ComNets-Bremen/WUSN/PCB-Enclosures/MoleNet_v6/Mounting_Plate/readme.txt

only Simple_Molenet_V6_Mount_Single_Screw_Pillars.stl tested. 
printed with 15% infill no support needed.
