ComNets-Bremen/WUSN/src/ATMEGA-based/MoleNet_2.0/decagon_5tm/README.md

# Decagon 5TM sensor Libarary

The library for temperature and volumetric content of water sensor, Decagon 5TM

### Version
1.0.0
