ComNets-Bremen/WUSN/src/ATMEGA-based/MoleNet_2.0/external_eeprom/README.md

# MoleNet Sensor Node EEPROM Libarary

The library external EEPROM (25LC1024) operations related to MoleNet Sensor Node.

### Version
1.0.0
