ComNets-Bremen/WUSN/src/ATMEGA-based/MoleNet_2.0/molenet_sensor_node/README.md

# Main MoleNet Sensor Node Libarary

The main library for MolneNet Sensor Node. It conatins all the functionalities 
of Multihop routing.

### Version
1.0.0
