ComNets-Bremen/WUSN/PCB-Layouts/MoleNet_v6.1/Readme.md

This folder contain Kicad files of Molenet V6.1 Board.
