ComNets-Bremen/WUSN/src/ATMEGA-based/MoleNet_2.0/serial_print/README.md

# Optimized Serial Print

A RAM optimized Serial print for Arduino. `Serial.print()` function in arduino consume
RAM to print the strings. These files provides method to print strings by storing 
then in program memory. More details can found in this like.

    http://www.utopiamechanicus.com/article/low-memory-serial-print/

### Version
1.0.0
