ComNets-Bremen/WUSN/experiments/LoRa_Gateway_for_WUSN/Modified Libraries/README.md

# Modified Libraries

This folder contains the RFM69 library modified, to work on a LoPy4.
Find the original library here: https://github.com/LowPowerLab/RFM69
