ComNets-Bremen/WUSN/experiments/LoRa_Gateway_for_WUSN/Field_Experiment/Field_experiment_2020_06_12.ods

jsonData.app_id | jsonData.dev_id | jsonData.hardware_serial | jsonData.port | jsonData.counter | jsonData.payload_raw | jsonData.payload_decoded | jsonData.metadata.time | jsonData.metadata.frequency | jsonData.metadata.modulation | jsonData.metadata.data_rate | jsonData.metadata.coding_rate | jsonData.metadata.downlink_url | gateway.gtw_id | gateway.timestamp | gateway.channel | gateway.rssi | gateway.snr | gateway.latitude | gateway.longitude | gateway.altitude | gateway.gtw_id | gateway.timestamp | gateway.channel | gateway.rssi | gateway.snr | gateway.latitude | gateway.longitude | gateway.altitude | gateway.gtw_id | gateway.timestamp | gateway.channel | gateway.rssi | gateway.snr | gateway.latitude | gateway.longitude | gateway.altitude
test_04_02_19 | pycomarduino | 0058924AB98D5AD4 | 1 | 0 | TW9pbgAAAAAAAAAAAAAAAAAAAAAAAAAAAAAAAAAAAAAAAAAAAAAAAA== | Moin | 2020-06-12T15:04:56.676741706Z | 867,3 | LORA | SF7BW125 | 4/5 | undefined | eui-fcc23dfffe0b696a | 2011301563 | 4 | -117 | -6,2 | undefined | undefined | undefined | eui-b827ebfffef74e1a | 1101593699 | 4 | -81 | 9,8 | undefined | undefined | undefined
test_04_02_19 | pycomarduino | 0058924AB98D5AD4 | 1 | 1 | WzJdIEQyMC8wNS8xOCB0MTI6MDAgVzAwMDAgVDAwMDAgPyAxICAgAA== | [2] D20/05/18 t12:00 W0000 T0000 ? 1 | 2020-06-12T15:05:29.272881041Z | 868,1 | LORA | SF7BW125 | 4/5 | undefined | eui-fcc23dfffe0b696a | 2043860939 | 0 | -117 | -4 | undefined | undefined | undefined | eui-b827ebfffef74e1a | 1134153083 | 0 | -82 | 9,2 | undefined | undefined | undefined
test_04_02_19 | pycomarduino | 0058924AB98D5AD4 | 1 | 2 | WzNdIEQyMC8wNS8xOCB0MTI6MDAgVzAwMDAgVDAwMDAgPyAxICAgAA== | [3] D20/05/18 t12:00 W0000 T0000 ? 1 | 2020-06-12T15:06:55.994188636Z | 868,3 | LORA | SF7BW125 | 4/5 | undefined | eui-b827ebfffef74e1a | 1220915163 | 1 | -84 | 9 | undefined | undefined | undefined
test_04_02_19 | pycomarduino | 0058924AB98D5AD4 | 1 | 3 | WzRdIEQyMC8wNS8xOCB0MTI6MDAgVzAwMDAgVDAwMDAgPyAxICAgAA== | [4] D20/05/18 t12:00 W0000 T0000 ? 1 | 2020-06-12T15:08:07.594137698Z | 867,5 | LORA | SF7BW125 | 4/5 | undefined | eui-fcc23dfffe0b696a | 2202222652 | 5 | -116 | -4 | undefined | undefined | undefined | eui-b827ebfffef74e1a | 1292514876 | 5 | -81 | 7 | undefined | undefined | undefined
test_04_02_19 | pycomarduino | 0058924AB98D5AD4 | 1 | 4 | WzVdIEQyMC8wNS8xOCB0MTI6MDAgVzAwMDAgVDAwMDAgPyAxICAgAA== | [5] D20/05/18 t12:00 W0000 T0000 ? 1 | 2020-06-12T15:09:34.050602207Z | 868,5 | LORA | SF7BW125 | 4/5 | undefined | eui-fcc23dfffe0b696a | 2288667515 | 2 | -112 | -2 | undefined | undefined | undefined | eui-b827ebfffef74e1a | 1378959771 | 2 | -83 | 7,8 | undefined | undefined | undefined
test_04_02_19 | pycomarduino | 0058924AB98D5AD4 | 1 | 5 | WzJdIEQyMC8wNS8xOCB0MTI6MDAgVzAwMDAgVDAwMDAgPyAxICAgAA== | [2] D20/05/18 t12:00 W0000 T0000 ? 1 | 2020-06-12T16:05:29.255052341Z | 868,1 | LORA | SF7BW125 | 4/5 | undefined | eui-b827ebfffef74e1a | 439193619 | 0 | -85 | 10 | undefined | undefined | undefined
test_04_02_19 | pycomarduino | 0058924AB98D5AD4 | 1 | 6 | WzNdIEQyMC8wNS8xOCB0MTI6MDAgVzAwMDAgVDAwMDAgPyAxICAgAA== | [3] D20/05/18 t12:00 W0000 T0000 ? 1 | 2020-06-12T16:06:55.988793539Z | 867,7 | LORA | SF7BW125 | 4/5 | undefined | eui-fcc23dfffe0b696a | 1435643132 | 6 | -113 | -4 | undefined | undefined | undefined | eui-b827ebfffef74e1a | 525936972 | 6 | -83 | 9,2 | undefined | undefined | undefined
test_04_02_19 | pycomarduino | 0058924AB98D5AD4 | 1 | 7 | WzRdIEQyMC8wNS8xOCB0MTI6MDAgVzAwMDAgVDAwMDAgPyAxICAgAA== | [4] D20/05/18 t12:00 W0000 T0000 ? 1 | 2020-06-12T16:08:07.601479262Z | 868,3 | LORA | SF7BW125 | 4/5 | undefined | eui-b827ebfffef74e1a | 597545867 | 1 | -83 | 9,2 | undefined | undefined | undefined
test_04_02_19 | pycomarduino | 0058924AB98D5AD4 | 1 | 8 | WzVdIEQyMC8wNS8xOCB0MTI6MDAgVzAwMDAgVDAwMDAgPyAxICAgAA== | [5] D20/05/18 t12:00 W0000 T0000 ? 1 | 2020-06-12T16:09:34.045542755Z | 868,5 | LORA | SF7BW125 | 4/5 | undefined | eui-fcc23dfffe0b696a | 1593703123 | 2 | -112 | -0,2 | undefined | undefined | undefined | eui-b827ebfffef74e1a | 683997035 | 2 | -81 | 7,8 | undefined | undefined | undefined
test_04_02_19 | pycomarduino | 0058924AB98D5AD4 | 1 | 9 | WzVdIEQyMC8wNS8xOCB0MTI6MDAgVzAwMDAgVDAwMDAgPyAxICAgAA== | [5] D20/05/18 t12:00 W0000 T0000 ? 1 | 2020-06-12T17:21:05.049491599Z | 867,9 | LORA | SF7BW125 | 4/5 | undefined | eui-fcc23dfffe0a9698 | 1591886324 | 7 | -116 | -5,5 | undefined | undefined | undefined | eui-b827ebfffef74e1a | 680034476 | 7 | -85 | 10,2 | undefined | undefined | undefined
test_04_02_19 | pycomarduino | 0058924AB98D5AD4 | 1 | 10 | WzVdIEQyMC8wNS8xOCB0MTI6MDAgVzAwMDAgVDAwMDAgPyAxICAgAA== | [5] D20/05/18 t12:00 W0000 T0000 ? 1 | 2020-06-12T18:32:39.87590631Z | 868,1 | LORA | SF7BW125 | 4/5 | undefined | eui-fcc23dfffe0b696a | 1589587211 | 0 | -117 | -1,8 | undefined | undefined | undefined | eui-b827ebfffef74e1a | 679885035 | 0 | -84 | 9,5 | undefined | undefined | undefined
test_04_02_19 | pycomarduino | 0058924AB98D5AD4 | 1 | 11 | WzJdIEQyMC8wNS8xOCB0MTI6MDAgVzAwMDAgVDAwMDAgPyAxICAgAA== | [2] D20/05/18 t12:00 W0000 T0000 ? 1 | 2020-06-12T19:05:29.263679511Z | 868,3 | LORA | SF7BW125 | 4/5 | undefined | eui-b827ebfffef74e1a | 2649283859 | 1 | -81 | 9,8 | undefined | undefined | undefined
test_04_02_19 | pycomarduino | 0058924AB98D5AD4 | 1 | 12 | WzNdIEQyMC8wNS8xOCB0MTI6MDAgVzAwMDAgVDAwMDAgPyAxICAgAA== | [3] D20/05/18 t12:00 W0000 T0000 ? 1 | 2020-06-12T19:06:55.94949052Z | 867,1 | LORA | SF7BW125 | 4/5 | undefined | eui-fcc23dfffe0a9698 | 3647817851 | 3 | -117 | -5 | undefined | undefined | undefined | eui-fcc23dfffe0b696a | 3645671747 | 3 | -117 | -0,5 | undefined | undefined | undefined | eui-b827ebfffef74e1a | 2735970507 | 3 | -89 | 11 | undefined | undefined | undefined
test_04_02_19 | pycomarduino | 0058924AB98D5AD4 | 1 | 13 | WzRdIEQyMC8wNS8xOCB0MTI6MDAgVzAwMDAgVDAwMDAgPyAxICAgAA== | [4] D20/05/18 t12:00 W0000 T0000 ? 1 | 2020-06-12T19:08:07.598150806Z | 868,5 | LORA | SF7BW125 | 4/5 | undefined | eui-b827ebfffef74e1a | 2807605883 | 2 | -80 | 7,2 | undefined | undefined | undefined
test_04_02_19 | pycomarduino | 0058924AB98D5AD4 | 1 | 14 | WzVdIEQyMC8wNS8xOCB0MTI6MDAgVzAwMDAgVDAwMDAgPyAxICAgAA== | [5] D20/05/18 t12:00 W0000 T0000 ? 1 | 2020-06-12T19:09:34.056058936Z | 868,1 | LORA | SF7BW125 | 4/5 | undefined | eui-b827ebfffef74e1a | 2894068995 | 0 | -84 | 9,8 | undefined | undefined | undefined
test_04_02_19 | pycomarduino | 0058924AB98D5AD4 | 1 | 15 | WzVdIEQyMC8wNS8xOCB0MTI6MDAgVzAwMDAgVDAwMDAgPyAxICAgAA== | [5] D20/05/18 t12:00 W0000 T0000 ? 1 | 2020-06-12T20:21:01.304674464Z | 867,3 | LORA | SF7BW125 | 4/5 | undefined | eui-fcc23dfffe0a9698 | 3798202899 | 4 | -116 | -7,8 | undefined | undefined | undefined | eui-fcc23dfffe0b696a | 3796057891 | 4 | -113 | -0,2 | undefined | undefined | undefined | eui-b827ebfffef74e1a | 2886358707 | 4 | -84 | 10 | undefined | undefined | undefined
test_04_02_19 | pycomarduino | 0058924AB98D5AD4 | 1 | 16 | WzVdIEQyMC8wNS8xOCB0MTI6MDAgVzAwMDAgVDAwMDAgPyAxICAgAA== | [5] D20/05/18 t12:00 W0000 T0000 ? 1 | 2020-06-12T21:32:32.91198065Z | 868,3 | LORA | SF7BW125 | 4/5 | undefined | eui-fcc23dfffe0b696a | 3792697227 | 1 | -113 | -3,8 | undefined | undefined | undefined | eui-b827ebfffef74e1a | 2882999995 | 1 | -83 | 10,2 | undefined | undefined | undefined
test_04_02_19 | pycomarduino | 0058924AB98D5AD4 | 1 | 17 | WzJdIEQyMC8wNS8xOCB0MTI6MDAgVzAwMDAgVDAwMDAgPyAxICAgAA== | [2] D20/05/18 t12:00 W0000 T0000 ? 1 | 2020-06-12T22:05:29.287404391Z | 868,5 | LORA | SF7BW125 | 4/5 | undefined | eui-fcc23dfffe0b696a | 1474103859 | 2 | -111 | 2 | undefined | undefined | undefined | eui-b827ebfffef74e1a | 564407523 | 2 | -81 | 7,8 | undefined | undefined | undefined
test_04_02_19 | pycomarduino | 0058924AB98D5AD4 | 1 | 18 | WzNdIEQyMC8wNS8xOCB0MTI6MDAgVzAwMDAgVDAwMDAgPyAxICAgAA== | [3] D20/05/18 t12:00 W0000 T0000 ? 1 | 2020-06-12T22:06:55.918812572Z | 867,5 | LORA | SF7BW125 | 4/5 | undefined | eui-fcc23dfffe0b696a | 1560732596 | 5 | -112 | -1,2 | undefined | undefined | undefined | eui-b827ebfffef74e1a | 651036300 | 5 | -83 | 8,2 | undefined | undefined | undefined
test_04_02_19 | pycomarduino | 0058924AB98D5AD4 | 1 | 19 | WzRdIEQyMC8wNS8xOCB0MTI6MDAgVzAwMDAgVDAwMDAgPyAxICAgAA== | [4] D20/05/18 t12:00 W0000 T0000 ? 1 | 2020-06-12T22:08:07.582433212Z | 868,1 | LORA | SF7BW125 | 4/5 | undefined | eui-fcc23dfffe0b696a | 1632394187 | 0 | -115 | -2,8 | undefined | undefined | undefined | eui-b827ebfffef74e1a | 722697915 | 0 | -84 | 10,8 | undefined | undefined | undefined
test_04_02_19 | pycomarduino | 0058924AB98D5AD4 | 1 | 20 | WzVdIEQyMC8wNS8xOCB0MTI6MDAgVzAwMDAgVDAwMDAgPyAxICAgAA== | [5] D20/05/18 t12:00 W0000 T0000 ? 1 | 2020-06-12T22:09:34.052301362Z | 868,3 | LORA | SF7BW125 | 4/5 | undefined | eui-fcc23dfffe0b696a | 1718869131 | 1 | -105 | 1,5 | undefined | undefined | undefined | eui-b827ebfffef74e1a | 809172899 | 1 | -81 | 9,8 | undefined | undefined | undefined
test_04_02_19 | pycomarduino | 0058924AB98D5AD4 | 1 | 21 | WzVdIEQyMC8wNS8xOCB0MTI6MDAgVzAwMDAgVDAwMDAgPyAxICAgAA== | [5] D20/05/18 t12:00 W0000 T0000 ? 1 | 2020-06-12T23:21:00.383448831Z | 867,7 | LORA | SF7BW125 | 4/5 | undefined | eui-b827ebfffef74e1a | 800529868 | 6 | -82 | 8,2 | undefined | undefined | undefined
test_04_02_19 | pycomarduino | 0058924AB98D5AD4 | 1 | 22 | WzVdIEQyMC8wNS8xOCB0MTI6MDAgVzAwMDAgVDAwMDAgPyAxICAgAA== | [5] D20/05/18 t12:00 W0000 T0000 ? 1 | 2020-06-13T00:32:30.636119936Z | 868,5 | LORA | SF7BW125 | 4/5 | undefined | eui-fcc23dfffe0b696a | 1705506987 | 2 | -112 | -2 | undefined | undefined | undefined | eui-b827ebfffef74e1a | 795814563 | 2 | -82 | 8,2 | undefined | undefined | undefined
test_04_02_19 | pycomarduino | 0058924AB98D5AD4 | 1 | 23 | WzJdIEQyMC8wNS8xOCB0MTI6MDAgVzAwMDAgVDAwMDAgPyAxICAgAA== | [2] D20/05/18 t12:00 W0000 T0000 ? 1 | 2020-06-13T01:05:29.312525431Z | 868,1 | LORA | SF7BW125 | 4/5 | undefined | eui-b827ebfffef74e1a | 2774495755 | 0 | -84 | 9,2 | undefined | undefined | undefined
test_04_02_19 | pycomarduino | 0058924AB98D5AD4 | 1 | 24 | WzNdIEQyMC8wNS8xOCB0MTI6MDAgVzAwMDAgVDAwMDAgPyAxICAgAA== | [3] D20/05/18 t12:00 W0000 T0000 ? 1 | 2020-06-13T01:06:55.893936757Z | 867,9 | LORA | SF7BW125 | 4/5 | undefined | eui-fcc23dfffe0b696a | 3770757604 | 7 | -116 | -3,8 | undefined | undefined | undefined | eui-b827ebfffef74e1a | 2861066076 | 7 | -87 | 9,5 | undefined | undefined | undefined
test_04_02_19 | pycomarduino | 0058924AB98D5AD4 | 1 | 25 | WzRdIEQyMC8wNS8xOCB0MTI6MDAgVzAwMDAgVDAwMDAgPyAxICAgAA== | [4] D20/05/18 t12:00 W0000 T0000 ? 1 | 2020-06-13T01:08:07.566586655Z | 868,3 | LORA | SF7BW125 | 4/5 | undefined | eui-b827ebfffef74e1a | 2932753875 | 1 | -83 | 10 | undefined | undefined | undefined
test_04_02_19 | pycomarduino | 0058924AB98D5AD4 | 1 | 26 | WzVdIEQyMC8wNS8xOCB0MTI6MDAgVzAwMDAgVDAwMDAgPyAxICAgAA== | [5] D20/05/18 t12:00 W0000 T0000 ? 1 | 2020-06-13T01:09:34.06488205Z | 868,5 | LORA | SF7BW125 | 4/5 | undefined | eui-b827ebfffef74e1a | 3019240427 | 2 | -83 | 7,8 | undefined | undefined | undefined
test_04_02_19 | pycomarduino | 0058924AB98D5AD4 | 1 | 27 | WzVdIEQyMC8wNS8xOCB0MTI6MDAgVzAwMDAgVDAwMDAgPyAxICAgAA== | [5] D20/05/18 t12:00 W0000 T0000 ? 1 | 2020-06-13T02:20:56.05140405Z | 867,1 | LORA | SF7BW125 | 4/5 | undefined | eui-fcc23dfffe0a9698 | 3918102363 | 3 | -116 | -6,5 | undefined | undefined | undefined | eui-fcc23dfffe0b696a | 3915962563 | 3 | -116 | -1,2 | undefined | undefined | undefined | eui-b827ebfffef74e1a | 3006272939 | 3 | -85 | 9,5 | undefined | undefined | undefined
test_04_02_19 | pycomarduino | 0058924AB98D5AD4 | 1 | 28 | WzVdIEQyMC8wNS8xOCB0MTI6MDAgVzAwMDAgVDAwMDAgPyAxICAgAA== | [5] D20/05/18 t12:00 W0000 T0000 ? 1 | 2020-06-13T03:32:24.678205638Z | 868,1 | LORA | SF7BW125 | 4/5 | undefined | eui-b827ebfffef74e1a | 2999922915 | 0 | -82 | 9 | undefined | undefined | undefined
test_04_02_19 | pycomarduino | 0058924AB98D5AD4 | 1 | 29 | WzJdIEQyMC8wNS8xOCB0MTI6MDAgVzAwMDAgVDAwMDAgPyAxICAgAA== | [2] D20/05/18 t12:00 W0000 T0000 ? 1 | 2020-06-13T04:05:29.332817207Z | 868,3 | LORA | SF7BW125 | 4/5 | undefined | eui-b827ebfffef74e1a | 689618019 | 1 | -83 | 9,2 | undefined | undefined | undefined
test_04_02_19 | pycomarduino | 0058924AB98D5AD4 | 1 | 30 | WzNdIEQyMC8wNS8xOCB0MTI6MDAgVzAwMDAgVDAwMDAgPyAxICAgAA== | [3] D20/05/18 t12:00 W0000 T0000 ? 1 | 2020-06-13T04:06:55.84183936Z | 867,3 | LORA | SF7BW125 | 4/5 | undefined | eui-fcc23dfffe0b696a | 1685816123 | 4 | -112 | 0 | undefined | undefined | undefined | eui-b827ebfffef74e1a | 776129171 | 4 | -85 | 9,8 | undefined | undefined | undefined
test_04_02_19 | pycomarduino | 0058924AB98D5AD4 | 1 | 31 | WzRdIEQyMC8wNS8xOCB0MTI6MDAgVzAwMDAgVDAwMDAgPyAxICAgAA== | [4] D20/05/18 t12:00 W0000 T0000 ? 1 | 2020-06-13T04:08:07.556456043Z | 868,5 | LORA | SF7BW125 | 4/5 | undefined | eui-fcc23dfffe0a9698 | 1759668403 | 2 | -113 | -8,2 | undefined | undefined | undefined | eui-fcc23dfffe0b696a | 1757530195 | 2 | -112 | -1 | undefined | undefined | undefined | eui-b827ebfffef74e1a | 847843267 | 2 | -80 | 7 | undefined | undefined | undefined
test_04_02_19 | pycomarduino | 0058924AB98D5AD4 | 1 | 32 | WzVdIEQyMC8wNS8xOCB0MTI6MDAgVzAwMDAgVDAwMDAgPyAxICAgAA== | [5] D20/05/18 t12:00 W0000 T0000 ? 1 | 2020-06-13T04:09:34.060531823Z | 868,1 | LORA | SF7BW125 | 4/5 | undefined | eui-fcc23dfffe0b696a | 1844028411 | 0 | -115 | -4,8 | undefined | undefined | undefined | eui-b827ebfffef74e1a | 934341515 | 0 | -83 | 9,8 | undefined | undefined | undefined
test_04_02_19 | pycomarduino | 0058924AB98D5AD4 | 1 | 33 | WzVdIEQyMC8wNS8xOCB0MTI6MDAgVzAwMDAgVDAwMDAgPyAxICAgAA== | [5] D20/05/18 t12:00 W0000 T0000 ? 1 | 2020-06-13T05:20:56.244774296Z | 867,5 | LORA | SF7BW125 | 4/5 | undefined | eui-fcc23dfffe0b696a | 1831248988 | 5 | -112 | -3,2 | undefined | undefined | undefined | eui-b827ebfffef74e1a | 921563900 | 5 | -85 | 7,2 | undefined | undefined | undefined
test_04_02_19 | pycomarduino | 0058924AB98D5AD4 | 1 | 34 | WzVdIEQyMC8wNS8xOCB0MTI6MDAgVzAwMDAgVDAwMDAgPyAxICAgAA== | [5] D20/05/18 t12:00 W0000 T0000 ? 1 | 2020-06-13T06:32:24.231663194Z | 868,3 | LORA | SF7BW125 | 4/5 | undefined | eui-fcc23dfffe0b696a | 1824268339 | 1 | -112 | -1,5 | undefined | undefined | undefined | eui-b827ebfffef74e1a | 914585115 | 1 | -80 | 9,5 | undefined | undefined | undefined
test_04_02_19 | pycomarduino | 0058924AB98D5AD4 | 1 | 35 | WzJdIEQyMC8wNS8xOCB0MTI6MDAgVzAwMDAgVDAwMDAgPyAxICAgAA== | [2] D20/05/18 t12:00 W0000 T0000 ? 1 | 2020-06-13T07:05:29.3548985Z | 868,5 | LORA | SF7BW125 | 4/5 | undefined | eui-fcc23dfffe0b696a | 3809387403 | 2 | -111 | 0,8 | undefined | undefined | undefined | eui-b827ebfffef74e1a | 2899705067 | 2 | -80 | 7,8 | undefined | undefined | undefined
test_04_02_19 | pycomarduino | 0058924AB98D5AD4 | 1 | 36 | WzNdIEQyMC8wNS8xOCB0MTI6MDAgVzAwMDAgVDAwMDAgPyAxICAgAA== | [3] D20/05/18 t12:00 W0000 T0000 ? 1 | 2020-06-13T07:06:55.860422855Z | 867,7 | LORA | SF7BW125 | 4/5 | undefined | eui-b827ebfffef74e1a | 2986157332 | 6 | -83 | 9,8 | undefined | undefined | undefined
test_04_02_19 | pycomarduino | 0058924AB98D5AD4 | 1 | 37 | WzRdIEQyMC8wNS8xOCB0MTI6MDAgVzAwMDAgVDAwMDAgPyAxICAgAA== | [4] D20/05/18 t12:00 W0000 T0000 ? 1 | 2020-06-13T07:08:07.554054722Z | 868,1 | LORA | SF7BW125 | 4/5 | undefined | eui-fcc23dfffe0b696a | 3967580563 | 0 | -117 | -4,8 | undefined | undefined | undefined | eui-b827ebfffef74e1a | 3057898307 | 0 | -85 | 9,8 | undefined | undefined | undefined
test_04_02_19 | pycomarduino | 0058924AB98D5AD4 | 1 | 38 | WzVdIEQyMC8wNS8xOCB0MTI6MDAgVzAwMDAgVDAwMDAgPyAxICAgAA== | [5] D20/05/18 t12:00 W0000 T0000 ? 1 | 2020-06-13T07:09:34.063335579Z | 868,3 | LORA | SF7BW125 | 4/5 | undefined | eui-fcc23dfffe0b696a | 4054090227 | 1 | -113 | -2,5 | undefined | undefined | undefined | eui-b827ebfffef74e1a | 3144408011 | 1 | -84 | 9,5 | undefined | undefined | undefined
test_04_02_19 | pycomarduino | 0058924AB98D5AD4 | 1 | 39 | WzJdIEQyMC8wNS8xOCB0MTI6MDAgVzAwMDAgVDAwMDAgPyAxICAgAA== | [2] D20/05/18 t12:00 W0000 T0000 ? 1 | 2020-06-13T08:05:29.362372982Z | 867,9 | LORA | SF7BW125 | 4/5 | undefined | eui-fcc23dfffe0b696a | 3114427308 | 7 | -117 | -3 | undefined | undefined | undefined | eui-b827ebfffef74e1a | 2204746620 | 7 | -85 | 10,5 | undefined | undefined | undefined
test_04_02_19 | pycomarduino | 0058924AB98D5AD4 | 1 | 40 | WzNdIEQyMC8wNS8xOCB0MTI6MDAgVzAwMDAgVDAwMDAgPyAxICAgAA== | [3] D20/05/18 t12:00 W0000 T0000 ? 1 | 2020-06-13T08:06:55.796875119Z | 868,5 | LORA | SF7BW125 | 4/5 | undefined | eui-fcc23dfffe0b696a | 3200860539 | 2 | -112 | 1,2 | undefined | undefined | undefined | eui-b827ebfffef74e1a | 2291179891 | 2 | -83 | 8,2 | undefined | undefined | undefined
test_04_02_19 | pycomarduino | 0058924AB98D5AD4 | 1 | 41 | WzRdIEQyMC8wNS8xOCB0MTI6MDAgVzAwMDAgVDAwMDAgPyAxICAgAA== | [4] D20/05/18 t12:00 W0000 T0000 ? 1 | 2020-06-13T08:08:07.544424964Z | 868,1 | LORA | SF7BW125 | 4/5 | undefined | eui-fcc23dfffe0b696a | 3272610443 | 0 | -116 | -2,8 | undefined | undefined | undefined | eui-b827ebfffef74e1a | 2362929827 | 0 | -85 | 9,5 | undefined | undefined | undefined
test_04_02_19 | pycomarduino | 0058924AB98D5AD4 | 1 | 42 | WzVdIEQyMC8wNS8xOCB0MTI6MDAgVzAwMDAgVDAwMDAgPyAxICAgAA== | [5] D20/05/18 t12:00 W0000 T0000 ? 1 | 2020-06-13T08:09:34.058278605Z | 867,1 | LORA | SF7BW125 | 4/5 | undefined | eui-fcc23dfffe0a9698 | 3361258531 | 3 | -117 | -7 | undefined | undefined | undefined | eui-fcc23dfffe0b696a | 3359123771 | 3 | -114 | -1,2 | undefined | undefined | undefined | eui-b827ebfffef74e1a | 2449443203 | 3 | -87 | 9,2 | undefined | undefined | undefined
test_04_02_19 | pycomarduino | 0058924AB98D5AD4 | 1 | 43 | WzVdIEQyMC8wNS8xOCB0MTI6MDAgVzAwMDAgVDAwMDAgPyAxICAgAA== | [5] D20/05/18 t12:00 W0000 T0000 ? 1 | 2020-06-13T09:20:59.247299721Z | 868,3 | LORA | SF7BW125 | 4/5 | undefined | eui-b827ebfffef74e1a | 2439661731 | 1 | -81 | 9 | undefined | undefined | undefined
test_04_02_19 | pycomarduino | 0058924AB98D5AD4 | 1 | 44 | WzJdIEQyMC8wNS8xOCB0MTI6MDAgVzAwMDAgVDAwMDAgPyAxICAgAA== | [2] D20/05/18 t12:00 W0000 T0000 ? 1 | 2020-06-13T10:05:29.377044179Z | 868,5 | LORA | SF7BW125 | 4/5 | undefined | eui-fcc23dfffe0b696a | 1724505787 | 2 | -112 | -0,2 | undefined | undefined | undefined | eui-b827ebfffef74e1a | 814828315 | 2 | -81 | 6,8 | undefined | undefined | undefined
test_04_02_19 | pycomarduino | 0058924AB98D5AD4 | 1 | 45 | WzNdIEQyMC8wNS8xOCB0MTI6MDAgVzAwMDAgVDAwMDAgPyAxICAgAA== | [3] D20/05/18 t12:00 W0000 T0000 ? 1 | 2020-06-13T10:06:55.772784111Z | 867,3 | LORA | SF7BW125 | 4/5 | undefined | eui-fcc23dfffe0b696a | 1810901667 | 4 | -113 | 0,2 | undefined | undefined | undefined | eui-b827ebfffef74e1a | 901224227 | 4 | -85 | 9,2 | undefined | undefined | undefined
test_04_02_19 | pycomarduino | 0058924AB98D5AD4 | 1 | 46 | WzRdIEQyMC8wNS8xOCB0MTI6MDAgVzAwMDAgVDAwMDAgPyAxICAgAA== | [4] D20/05/18 t12:00 W0000 T0000 ? 1 | 2020-06-13T10:08:07.537982354Z | 868,1 | LORA | SF7BW125 | 4/5 | undefined | eui-fcc23dfffe0b696a | 1882669347 | 0 | -117 | -3,2 | undefined | undefined | undefined | eui-b827ebfffef74e1a | 972991939 | 0 | -84 | 9,5 | undefined | undefined | undefined
test_04_02_19 | pycomarduino | 0058924AB98D5AD4 | 1 | 47 | WzVdIEQyMC8wNS8xOCB0MTI6MDAgVzAwMDAgVDAwMDAgPyAxICAgAA== | [5] D20/05/18 t12:00 W0000 T0000 ? 1 � | 2020-06-13T10:09:34.075162749Z | 868,3 | LORA | SF7BW125 | 4/5 | undefined | eui-b827ebfffef74e1a | 1059512411 | 1 | -83 | 10,2 | undefined | undefined | undefined
test_04_02_19 | pycomarduino | 0058924AB98D5AD4 | 1 | 48 | WzJdIEQyMC8wNS8xOCB0MTI6MDAgVzAwMDAgVDAwMDAgPyAxICAgAA== | [2] D20/05/18 t12:00 W0000 T0000 ? 1 | 2020-06-13T11:05:29.387017508Z | 867,5 | LORA | SF7BW125 | 4/5 | undefined | eui-fcc23dfffe0b696a | 1029544500 | 5 | -116 | -4,5 | undefined | undefined | undefined | eui-b827ebfffef74e1a | 119868532 | 5 | -83 | 7,5 | undefined | undefined | undefined
test_04_02_19 | pycomarduino | 0058924AB98D5AD4 | 1 | 49 | WzNdIEQyMC8wNS8xOCB0MTI6MDAgVzAwMDAgVDAwMDAgPyAxICAgAA== | [3] D20/05/18 t12:00 W0000 T0000 ? 1 | 2020-06-13T11:06:55.760968746Z | 868,5 | LORA | SF7BW125 | 4/5 | undefined | eui-fcc23dfffe0b696a | 1115921795 | 2 | -113 | -4,2 | undefined | undefined | undefined | eui-b827ebfffef74e1a | 206245867 | 2 | -83 | 7 | undefined | undefined | undefined
test_04_02_19 | pycomarduino | 0058924AB98D5AD4 | 1 | 50 | WzRdIEQyMC8wNS8xOCB0MTI6MDAgVzAwMDAgVDAwMDAgPyAxICAgAA== | [4] D20/05/18 t12:00 W0000 T0000 ? 1 | 2020-06-13T11:08:07.537219253Z | 868,1 | LORA | SF7BW125 | 4/5 | undefined | eui-fcc23dfffe0b696a | 1187698195 | 0 | -117 | -2,2 | undefined | undefined | undefined | eui-b827ebfffef74e1a | 278022299 | 0 | -82 | 9,8 | undefined | undefined | undefined
test_04_02_19 | pycomarduino | 0058924AB98D5AD4 | 1 | 51 | WzVdIEQyMC8wNS8xOCB0MTI6MDAgVzAwMDAgVDAwMDAgPyAxICAgAA== | [5] D20/05/18 t12:00 W0000 T0000 ? 1 | 2020-06-13T11:09:34.062948248Z | 867,7 | LORA | SF7BW125 | 4/5 | undefined | eui-fcc23dfffe0b696a | 1274222308 | 6 | -115 | -7 | undefined | undefined | undefined | eui-b827ebfffef74e1a | 364546436 | 6 | -84 | 8,8 | undefined | undefined | undefined
test_04_02_19 | pycomarduino | 0058924AB98D5AD4 | 1 | 52 | WzVdIEQyMC8wNS8xOCB0MTI6MDAgVzAwMDAgVDAwMDAgPyAxICAgAA== | [5] D20/05/18 t12:00 W0000 T0000 ? 1 | 2020-06-13T12:21:03.132162656Z | 868,3 | LORA | SF7BW125 | 4/5 | undefined | eui-b827ebfffef74e1a | 358652747 | 1 | -81 | 10,5 | undefined | undefined | undefined
test_04_02_19 | pycomarduino | 0058924AB98D5AD4 | 1 | 53 | WzVdIEQyMC8wNS8xOCB0MTI6MDAgVzAwMDAgVDAwMDAgPyAxICAgAA== | [5] D20/05/18 t12:00 W0000 T0000 ? 1 | 2020-06-13T13:32:43.836725387Z | 868,5 | LORA | SF7BW125 | 4/5 | undefined | eui-fcc23dfffe0a9698 | 1276191363 | 2 | -115 | -8 | undefined | undefined | undefined | eui-fcc23dfffe0b696a | 1274061795 | 2 | -111 | 0,5 | undefined | undefined | undefined | eui-b827ebfffef74e1a | 364389499 | 2 | -82 | 7,5 | undefined | undefined | undefined
test_04_02_19 | pycomarduino | 0058924AB98D5AD4 | 1 | 54 | WzJdIEQyMC8wNS8xOCB0MTI6MDAgVzAwMDAgVDAwMDAgPyAxICAgAA== | [2] D20/05/18 t12:00 W0000 T0000 ? 1 | 2020-06-13T14:05:29.408974789Z | 868,1 | LORA | SF7BW125 | 4/5 | undefined | eui-fcc23dfffe0b696a | 3239633515 | 0 | -117 | -5,2 | undefined | undefined | undefined | eui-b827ebfffef74e1a | 2329962083 | 0 | -85 | 10,2 | undefined | undefined | undefined
test_04_02_19 | pycomarduino | 0058924AB98D5AD4 | 1 | 55 | WzNdIEQyMC8wNS8xOCB0MTI6MDAgVzAwMDAgVDAwMDAgPyAxICAgAA== | [3] D20/05/18 t12:00 W0000 T0000 ? 1 | 2020-06-13T14:06:55.731635763Z | 867,9 | LORA | SF7BW125 | 4/5 | undefined | eui-fcc23dfffe0a9698 | 3328086092 | 7 | -117 | -7,2 | undefined | undefined | undefined | eui-fcc23dfffe0b696a | 3325957020 | 7 | -117 | -2,2 | undefined | undefined | undefined | eui-b827ebfffef74e1a | 2416285620 | 7 | -84 | 8,8 | undefined | undefined | undefined
test_04_02_19 | pycomarduino | 0058924AB98D5AD4 | 1 | 56 | WzRdIEQyMC8wNS8xOCB0MTI6MDAgVzAwMDAgVDAwMDAgPyAxICAgAA== | [4] D20/05/18 t12:00 W0000 T0000 ? 1 | 2020-06-13T14:08:07.541788077Z | 868,3 | LORA | SF7BW125 | 4/5 | undefined | eui-fcc23dfffe0b696a | 3397759371 | 1 | -109 | -1,5 | undefined | undefined | undefined | eui-b827ebfffef74e1a | 2488088003 | 1 | -84 | 10,2 | undefined | undefined | undefined
test_04_02_19 | pycomarduino | 0058924AB98D5AD4 | 1 | 57 | WzVdIEQyMC8wNS8xOCB0MTI6MDAgVzAwMDAgVDAwMDAgPyAxICAgAA== | [5] D20/05/18 t12:00 W0000 T0000 ? 1 | 2020-06-13T14:09:34.070767228Z | 868,5 | LORA | SF7BW125 | 4/5 | undefined | eui-fcc23dfffe0b696a | 3484294155 | 2 | -112 | -8,8 | undefined | undefined | undefined | eui-b827ebfffef74e1a | 2574622827 | 2 | -83 | 7,5 | undefined | undefined | undefined
test_04_02_19 | pycomarduino | 0058924AB98D5AD4 | 1 | 58 | WzVdIEQyMC8wNS8xOCB0MTI6MDAgVzAwMDAgVDAwMDAgPyAxICAgAA== | [5] D20/05/18 t12:00 W0000 T0000 ? 1 | 2020-06-13T15:21:09.734285963Z | 867,1 | LORA | SF7BW125 | 4/5 | undefined | eui-fcc23dfffe0a9698 | 3487114891 | 3 | -115 | -4,2 | undefined | undefined | undefined | eui-fcc23dfffe0b696a | 3484986979 | 3 | -115 | -2,5 | undefined | undefined | undefined | eui-b827ebfffef74e1a | 2575317587 | 3 | -89 | 9,8 | undefined | undefined | undefined
test_04_02_19 | pycomarduino | 0058924AB98D5AD4 | 1 | 59 | WzVdIEQyMC8wNS8xOCB0MTI6MDAgVzAwMDAgVDAwMDAgPyAxICAgAA== | [5] D20/05/18 t12:00 W0000 T0000 ? 1 | 2020-06-13T16:32:46.46953058Z | 868,1 | LORA | SF7BW125 | 4/5 | undefined | eui-b827ebfffef74e1a | 2577083187 | 0 | -84 | 9,8 | undefined | undefined | undefined
test_04_02_19 | pycomarduino | 0058924AB98D5AD4 | 1 | 60 | WzJdIEQyMC8wNS8xOCB0MTI6MDAgVzAwMDAgVDAwMDAgPyAxICAgAA== | [2] D20/05/18 t12:00 W0000 T0000 ? 1 | 2020-06-13T17:05:29.440291977Z | 868,3 | LORA | SF7BW125 | 4/5 | undefined | eui-b827ebfffef74e1a | 245088603 | 1 | -82 | 9,5 | undefined | undefined | undefined
test_04_02_19 | pycomarduino | 0058924AB98D5AD4 | 1 | 61 | WzNdIEQyMC8wNS8xOCB0MTI6MDAgVzAwMDAgVDAwMDAgPyAxICAgAA== | [3] D20/05/18 t12:00 W0000 T0000 ? 1 | 2020-06-13T17:06:55.718435075Z | 867,3 | LORA | SF7BW125 | 4/5 | undefined | eui-fcc23dfffe0b696a | 1241025443 | 4 | -113 | -2,2 | undefined | undefined | undefined | eui-b827ebfffef74e1a | 331359035 | 4 | -87 | 10,8 | undefined | undefined | undefined
test_04_02_19 | pycomarduino | 0058924AB98D5AD4 | 1 | 62 | WzRdIEQyMC8wNS8xOCB0MTI6MDAgVzAwMDAgVDAwMDAgPyAxICAgAA== | [4] D20/05/18 t12:00 W0000 T0000 ? 1 | 2020-06-13T17:08:07.535265778Z | 868,5 | LORA | SF7BW125 | 4/5 | undefined | eui-fcc23dfffe0b696a | 1312853043 | 2 | -113 | 0,8 | undefined | undefined | undefined | eui-b827ebfffef74e1a | 403186675 | 2 | -80 | 8 | undefined | undefined | undefined
test_04_02_19 | pycomarduino | 0058924AB98D5AD4 | 1 | 63 | WzVdIEQyMC8wNS8xOCB0MTI6MDAgVzAwMDAgVDAwMDAgPyAxICAgAA== | [5] D20/05/18 t12:00 W0000 T0000 ? 1 | 2020-06-13T17:09:34.086910172Z | 868,1 | LORA | SF7BW125 | 4/5 | undefined | eui-b827ebfffef74e1a | 489733675 | 0 | -82 | 8,5 | undefined | undefined | undefined
test_04_02_19 | pycomarduino | 0058924AB98D5AD4 | 1 | 64 | WzVdIEQyMC8wNS8xOCB0MTI6MDAgVzAwMDAgVDAwMDAgPyAxICAgAA== | [5] D20/05/18 t12:00 W0000 T0000 ? 1 | 2020-06-13T18:21:07.463129057Z | 867,5 | LORA | SF7BW125 | 4/5 | undefined | eui-fcc23dfffe0b696a | 1397806428 | 5 | -112 | 2 | undefined | undefined | undefined | eui-b827ebfffef74e1a | 488142124 | 5 | -85 | 8 | undefined | undefined | undefined
test_04_02_19 | pycomarduino | 0058924AB98D5AD4 | 1 | 65 | WzVdIEQyMC8wNS8xOCB0MTI6MDAgVzAwMDAgVDAwMDAgPyAxICAgAA== | [5] D20/05/18 t12:00 W0000 T0000 ? 1 | 2020-06-13T19:32:43.21336031Z | 868,3 | LORA | SF7BW125 | 4/5 | undefined | eui-b827ebfffef74e1a | 488928843 | 1 | -84 | 9,8 | undefined | undefined | undefined
test_04_02_19 | pycomarduino | 0058924AB98D5AD4 | 1 | 66 | WzJdIEQyMC8wNS8xOCB0MTI6MDAgVzAwMDAgVDAwMDAgPyAxICAgAA== | [2] D20/05/18 t12:00 W0000 T0000 ? 1 | 2020-06-13T20:05:29.475479549Z | 868,5 | LORA | SF7BW125 | 4/5 | undefined | eui-b827ebfffef74e1a | 2455183707 | 2 | -83 | 7,5 | undefined | undefined | undefined
test_04_02_19 | pycomarduino | 0058924AB98D5AD4 | 1 | 67 | WzNdIEQyMC8wNS8xOCB0MTI6MDAgVzAwMDAgVDAwMDAgPyAxICAgAA== | [3] D20/05/18 t12:00 W0000 T0000 ? 1 | 2020-06-13T20:06:55.681468966Z | 867,7 | LORA | SF7BW125 | 4/5 | undefined | eui-b827ebfffef74e1a | 2541398748 | 6 | -87 | 11 | undefined | undefined | undefined
test_04_02_19 | pycomarduino | 0058924AB98D5AD4 | 1 | 68 | WzRdIEQyMC8wNS8xOCB0MTI6MDAgVzAwMDAgVDAwMDAgPyAxICAgAA== | [4] D20/05/18 t12:00 W0000 T0000 ? 1 | 2020-06-13T20:08:07.534807586Z | 868,1 | LORA | SF7BW125 | 4/5 | undefined | eui-fcc23dfffe0b696a | 3522912427 | 0 | -119 | -3,2 | undefined | undefined | undefined | eui-b827ebfffef74e1a | 2613251131 | 0 | -85 | 11 | undefined | undefined | undefined
test_04_02_19 | pycomarduino | 0058924AB98D5AD4 | 1 | 69 | WzVdIEQyMC8wNS8xOCB0MTI6MDAgVzAwMDAgVDAwMDAgPyAxICAgAA== | [5] D20/05/18 t12:00 W0000 T0000 ? 1 | 2020-06-13T20:09:34.096525329Z | 868,3 | LORA | SF7BW125 | 4/5 | undefined | eui-b827ebfffef74e1a | 2699809523 | 1 | -83 | 10 | undefined | undefined | undefined
test_04_02_19 | pycomarduino | 0058924AB98D5AD4 | 1 | 70 | WzVdIEQyMC8wNS8xOCB0MTI6MDAgVzAwMDAgVDAwMDAgPyAxICAgAA== | [5] D20/05/18 t12:00 W0000 T0000 ? 1 | 2020-06-13T21:21:04.513180599Z | 867,9 | LORA | SF7BW125 | 4/5 | undefined | eui-fcc23dfffe0a9698 | 3607047868 | 7 | -117 | -4,2 | undefined | undefined | undefined | eui-fcc23dfffe0b696a | 3604925220 | 7 | -116 | -0,2 | undefined | undefined | undefined | eui-b827ebfffef74e1a | 2695265972 | 7 | -85 | 10,8 | undefined | undefined | undefined
test_04_02_19 | pycomarduino | 0058924AB98D5AD4 | 1 | 71 | WzVdIEQyMC8wNS8xOCB0MTI6MDAgVzAwMDAgVDAwMDAgPyAxICAgAA== | [5] D20/05/18 t12:00 W0000 T0000 ? 1 | 2020-06-13T22:32:38.58360693Z | 868,5 | LORA | SF7BW125 | 4/5 | undefined | eui-b827ebfffef74e1a | 2694362019 | 2 | -84 | 7 | undefined | undefined | undefined
test_04_02_19 | pycomarduino | 0058924AB98D5AD4 | 1 | 72 | WzJdIEQyMC8wNS8xOCB0MTI6MDAgVzAwMDAgVDAwMDAgPyAxICAgAA== | [2] D20/05/18 t12:00 W0000 T0000 ? 1 | 2020-06-13T23:05:29.498102001Z | 868,1 | LORA | SF7BW125 | 4/5 | undefined | eui-fcc23dfffe0b696a | 1279965003 | 0 | -116 | -6,8 | undefined | undefined | undefined | eui-b827ebfffef74e1a | 370308643 | 0 | -85 | 10,2 | undefined | undefined | undefined
test_04_02_19 | pycomarduino | 0058924AB98D5AD4 | 1 | 73 | WzNdIEQyMC8wNS8xOCB0MTI6MDAgVzAwMDAgVDAwMDAgPyAxICAgAA== | [3] D20/05/18 t12:00 W0000 T0000 ? 1 | 2020-06-13T23:06:55.649301534Z | 867,1 | LORA | SF7BW125 | 4/5 | undefined | eui-fcc23dfffe0a9698 | 1368244155 | 3 | -116 | -5,5 | undefined | undefined | undefined | eui-fcc23dfffe0b696a | 1366123027 | 3 | -113 | 1 | undefined | undefined | undefined | eui-b827ebfffef74e1a | 456466707 | 3 | -89 | 9,5 | undefined | undefined | undefined
test_04_02_19 | pycomarduino | 0058924AB98D5AD4 | 1 | 74 | WzRdIEQyMC8wNS8xOCB0MTI6MDAgVzAwMDAgVDAwMDAgPyAxICAgAA== | [4] D20/05/18 t12:00 W0000 T0000 ? 1 | 2020-06-13T23:08:07.534900631Z | 868,3 | LORA | SF7BW125 | 4/5 | undefined | eui-b827ebfffef74e1a | 528344035 | 1 | -83 | 9 | undefined | undefined | undefined
test_04_02_19 | pycomarduino | 0058924AB98D5AD4 | 1 | 75 | WzVdIEQyMC8wNS8xOCB0MTI6MDAgVzAwMDAgVDAwMDAgPyAxICAgAA== | [5] D20/05/18 t12:00 W0000 T0000 ? 1 | 2020-06-13T23:09:34.13932144Z | 868,5 | LORA | SF7BW125 | 4/5 | undefined | eui-fcc23dfffe0b696a | 1524569891 | 2 | -113 | 0,5 | undefined | undefined | undefined
 |  |  |  |  |  |  |  |  | LORA | SF7BW125 | 4/5 | undefined | eui-fcc23dfffe0b696a | 3722415452 | 5 | -115 | -5 | undefined | undefined | undefined | eui-b827ebfffef74e1a | 2812817316 | 5 | -80 | 9 | undefined | undefined | undefined
Werte empfangen gesamt: | 75 | Startzeit: | 12.06.20 | 15:04:56
Akkulaufzeit(T): | 1.34 | Endzeit: | 13.06.20 | 23:09:34
Akkulaufzeit(H): | 32.0772222221832
Erwartete Packete: | 132
Empfangene Pakete %: | 56.82%
