ComNets-Bremen/WUSN/PCB-Layouts/MoleNet_v2.1/MoleNet_v21_schematic.pdf

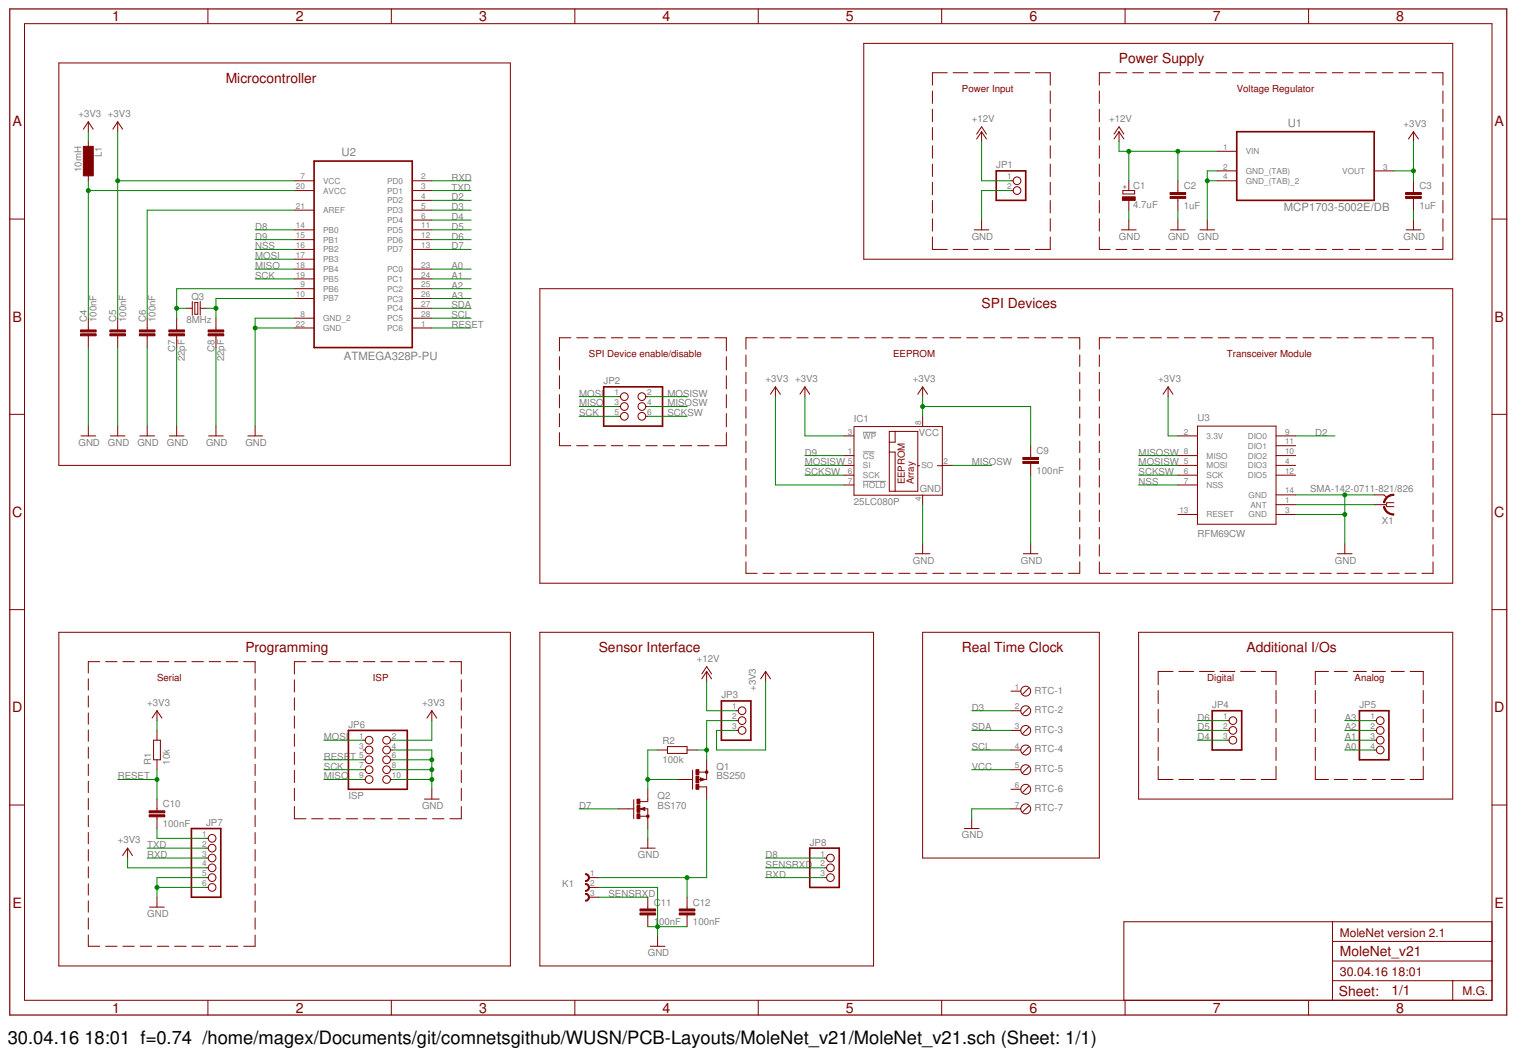
[picture p29: page 1]

30.04.16 18:01 f=0.74 /home/magex/Documents/git/comnetsgithub/WUSN/PCB-Layouts/MoleNet_v21/MoleNet_v21.sch (Sheet: 1/1)
