ComNets-Bremen/WUSN/src/ATMEGA-based/MoleNet_2.0/spirilis-spieep-a2e68061ce45/SPIEEP.h

/* Copyright (C) 2011 by Eric Brundick <spirilis@linux.com>
 * Distributed under the terms of the GNU Lesser General Public License
 * A copy of this license may be obtained at:
 * http://www.gnu.org/copyleft/lesser.html
 */


/* SPIEEP - A library to interface with Microchip 25LC512 SPI-accessible EEPROM chips.
 * Generalized to allow different address widths (multiple of 8 bits) along with different
 *   page sizes and capacities, so long as the instruction set works the same way.
 *
 * Utilizes Arduino's SPI library for its communication and works within the Arduino
 * framework (utilizing digitalWrite(), along with the 'byte' datatype)
 */

/* Example pinout for the 25LC512 chip:
                                           ---v---
             Arduino digital pin 10 <-  CS |     | Vcc (+2.5-5.5V)
  Arduino digital pin 12 (MISO) <-  SerOUT |     | HOLD -> Connected to Vcc (not used)
        Connected to Vcc (not used) <-  WP |     | SCK -> Arduino digital pin 13 (SCK)
                                 Vss (GND) |     | SerIN -> Arduino digital pin 11 (MOSI)
                                           -------

 * Note: WP is used for write protection, see the datasheet for details:
 *   http://ww1.microchip.com/downloads/en/DeviceDoc/22065C.pdf
 * HOLD is used to pause I/O mid-stream without losing place in the command sequence
 *   in case you have a higher-priority interrupt to handle. Not something I see myself using.
 */

#ifndef _SPIEEP_H_INCLUDED
#define _SPIEEP_H_INCLUDED

#if defined(ARDUINO) && ARDUINO < 100
  #include <WProgram.h>
#else
  #include <Arduino.h>
#endif

#include <avr/pgmspace.h>

class SPIEEP {
  private:
    uint8_t _cspin;
    uint16_t _pagesize;
    uint16_t _numpages;
    uint32_t _highestaddr;
    uint8_t _addrwidth;
    boolean _is_25LC040;
    boolean _write_validation();
    void _write_address(uint32_t);
    inline byte _compose_instruction_addrbit(uint32_t, byte);

  public:
    SPIEEP(uint8_t addrwidth, uint16_t pagesize, uint32_t totalsize);
    void begin(int cspin);
    void begin_spi(int cspin);
    void end();
    boolean verify_enabled();
    int pagesize();

    void wren();
    boolean is_wren();
    void wrdi();
    void dpd();
    byte rdid();
    void sleepmode();  // Alias of dpd()
    byte wakeup();     // Alias of rdid()
    byte readstatus();
    void writestatus(byte);
    boolean test_chip();  /* Run a bunch of tests on the chip
                           * to validate functionality
                           */

    /* byte-oriented functions (these are the core I/O functions) */
    byte read(uint32_t);
    boolean readn(uint32_t, byte *, uint16_t);
    boolean write(uint32_t, byte);
    boolean writen(uint32_t, byte *, uint16_t);
    boolean read_page(uint32_t, byte *);
    boolean write_page(uint32_t, byte *);

    /* char-casting versions of these functions */
    boolean readn(uint32_t, char *, uint16_t);
    boolean write(uint32_t, char);
    boolean writen(uint32_t, char *, uint16_t);
    boolean read_page(uint32_t, char *);
    boolean write_page(uint32_t, char *);

    /* Integer variants which address-translate */
    int read_int(uint32_t);
    boolean readn_int(uint32_t, int *, uint16_t);
    boolean write_int(uint32_t, int);
    boolean writen_int(uint32_t, int *, uint16_t);
    /* Offset variants - allow the use of an offset to adjust the origin address for
     *   all computed addresses (to facilitate partitioning of the memory among
     *   heterogeneous data types
     */
    int read_int_offset(uint32_t, uint32_t);
    boolean readn_int_offset(uint32_t, uint32_t, int *, uint16_t);
    boolean write_int_offset(uint32_t, uint32_t, int);
    boolean writen_int_offset(uint32_t, uint32_t, int *, uint16_t);

    /* Long-integer variants which address-translate */
    long read_long(uint32_t);
    boolean readn_long(uint32_t, long *, uint16_t);
    boolean write_long(uint32_t, long);
    boolean writen_long(uint32_t, long *, uint16_t);
    /* Offset variants */
    long read_long_offset(uint32_t, uint32_t);
    boolean readn_long_offset(uint32_t, uint32_t, long *, uint16_t);
    boolean write_long_offset(uint32_t, uint32_t, long);
    boolean writen_long_offset(uint32_t, uint32_t, long *, uint16_t);

    /* Float variants which address-translate */
    float read_float(uint32_t);
    boolean readn_float(uint32_t, float *, uint16_t);
    boolean write_float(uint32_t, float);
    boolean writen_float(uint32_t, float *, uint16_t);
    /* Offset variants */
    float read_float_offset(uint32_t, uint32_t);
    boolean readn_float_offset(uint32_t, uint32_t, float *, uint16_t);
    boolean write_float_offset(uint32_t, uint32_t, float);
    boolean writen_float_offset(uint32_t, uint32_t, float *, uint16_t);

    /* Double-wide float variants which address-translate */
    double read_double(uint32_t);
    boolean readn_double(uint32_t, double *, uint16_t);
    boolean write_double(uint32_t, double);
    boolean writen_double(uint32_t, double *, uint16_t);
    /* Offset variants */
    double read_double_offset(uint32_t, uint32_t);
    boolean readn_double_offset(uint32_t, uint32_t, double *, uint16_t);
    boolean write_double_offset(uint32_t, uint32_t, double);
    boolean writen_double_offset(uint32_t, uint32_t, double *, uint16_t);

    boolean chip_erase();
    boolean page_erase(uint32_t);
};

#endif
