ComNets-Bremen/WUSN/experiments/LoRa_Gateway_for_WUSN/Modified Libraries/RFM69_LowPowerLab/RFM69.h

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
#define RFM69_h
#include <Arduino.h>            // assumes Arduino IDE v1.0 or greater
#include <SPI.h>
 #if (MPIDE>=150 && defined(ARDUINO))
  #define RF69_PLATFORM RF69_PLATFORM_CHIPKIT_CORE
 #elif defined(MPIDE)
  #define RF69_PLATFORM RF69_PLATFORM_UNO32
#elif defined(NRF51)
  #define RF69_PLATFORM RF69_PLATFORM_NRF51
#elif defined(NRF52)
  #define RF69_PLATFORM RF69_PLATFORM_NRF52
 #elif defined(ESP8266)
  #define RF69_PLATFORM RF69_PLATFORM_ESP8266
 #elif defined(ESP32)
  #define RF69_PLATFORM RF69_PLATFORM_ESP32
 #elif defined(ARDUINO)
  #define RF69_PLATFORM RF69_PLATFORM_ARDUINO
 #elif defined(__MSP430G2452__) || defined(__MSP430G2553__)
  #define RF69_PLATFORM RF69_PLATFORM_MSP430
 #elif defined(MCU_STM32F103RE)
  #define RF69_PLATFORM RF69_PLATFORM_STM32
 #elif defined(STM32F2XX)
  #define RF69_PLATFORM RF69_PLATFORM_STM32F2
 #elif defined(USE_STDPERIPH_DRIVER)
  #define RF69_PLATFORM RF69_PLATFORM_STM32STD
 #elif defined(RASPBERRY_PI)
  #define RF69_PLATFORM RF69_PLATFORM_RASPI
#elif defined(__unix__) // Linux
  #define RF69_PLATFORM RF69_PLATFORM_UNIX
#elif defined(__APPLE__) // OSX
  #define RF69_PLATFORM RF69_PLATFORM_UNIX
 #else
  #error Platform not defined!
 #endif
 #define NOT_AN_INTERRUPT -1
 #if (RF69_PLATFORM == RF69_PLATFORM_ARDUINO) && !defined(__arm__)
  #if defined(__AVR_ATmega1280__) || defined(__AVR_ATmega2560__)
   #define digitalPinToInterrupt(p) ((p) == 2 ? 0 : ((p) == 3 ? 1 : ((p) >= 18 && (p) <= 21 ? 23 - (p) : NOT_AN_INTERRUPT)))
  #elif defined(__AVR_ATmega1284__) || defined(__AVR_ATmega1284P__)
   #define digitalPinToInterrupt(p) ((p) == 10 ? 0 : ((p) == 11 ? 1 : ((p) == 2 ? 2 : NOT_AN_INTERRUPT)))
  #elif defined(__AVR_ATmega32U4__)
   #define digitalPinToInterrupt(p) ((p) == 0 ? 2 : ((p) == 1 ? 3 : ((p) == 2 ? 1 : ((p) == 3 ? 0 : ((p) == 7 ? 4 : NOT_AN_INTERRUPT)))))
  #else
   #define digitalPinToInterrupt(p)  ((p) == 2 ? 0 : ((p) == 3 ? 1 : NOT_AN_INTERRUPT))
  #endif
 #elif (RF69_PLATFORM == RF69_PLATFORM_UNO32) || (RF69_PLATFORM == RF69_PLATFORM_CHIPKIT_CORE)
  #define digitalPinToInterrupt(p) ((p) == 38 ? 0 : ((p) == 2 ? 1 : ((p) == 7 ? 2 : ((p) == 8 ? 3 : ((p) == 735 ? 4 : NOT_AN_INTERRUPT)))))
 #else
  #define digitalPinToInterrupt(p) (p)
 #endif
#if (RF69_PLATFORM == RF69_PLATFORM_ARDUINO) && defined (__arm__) && (defined(ARDUINO_ARCH_SAMD) || defined(ARDUINO_SAM_DUE))
 #define RF69_ATTACHINTERRUPT_TAKES_PIN_NUMBER
#endif
#define RF69_SPI_CS             SS // SS is the SPI slave select pin, for instance D10 on ATmega328
#if defined(__AVR_ATmega168__) || defined(__AVR_ATmega328P__) || defined(__AVR_ATmega88) || defined(__AVR_ATmega8__) || defined(__AVR_ATmega88__)
  #define RF69_IRQ_PIN          2
#elif defined(__AVR_ATmega644P__) || defined(__AVR_ATmega1284P__)
  #define RF69_IRQ_PIN          2
#elif defined(__AVR_ATmega32U4__)
  #define RF69_IRQ_PIN          7
#elif defined(__STM32F1__)
  #define RF69_IRQ_PIN          PA3
#elif defined(MOTEINO_M0)
  #define RF69_IRQ_PIN          9
#elif defined(ARDUINO_SAMD_ZERO) //includes Feather SAMD
  #define RF69_IRQ_PIN          3
#else
  #define RF69_IRQ_PIN          2
#endif
#define RF69_MAX_DATA_LEN       61 // to take advantage of the built in AES/CRC we want to limit the frame size to the internal FIFO size (66 bytes - 3 bytes overhead - 2 bytes crc)
#define CSMA_LIMIT              -90 // upper RX signal sensitivity threshold in dBm for carrier sense access
#define RF69_MODE_SLEEP         0 // XTAL OFF
#define RF69_MODE_STANDBY       1 // XTAL ON
#define RF69_MODE_SYNTH         2 // PLL ON
#define RF69_MODE_RX            3 // RX MODE
#define RF69_MODE_TX            4 // TX MODE
#define RF69_315MHZ            31 // non trivial values to avoid misconfiguration
#define RF69_433MHZ            43
#define RF69_868MHZ            86
#define RF69_915MHZ            91
#define null                  0
#define COURSE_TEMP_COEF    -90 // puts the temperature reading in the ballpark, user can fine tune the returned value
#define RF69_BROADCAST_ADDR   0
#define RF69_CSMA_LIMIT_MS 1000
#define RF69_TX_LIMIT_MS   1000
#define RF69_FSTEP  61.03515625 // == FXOSC / 2^19 = 32MHz / 2^19 (p13 in datasheet)
#define RFM69_CTL_SENDACK   0x80
#define RFM69_CTL_REQACK    0x40
class RFM69 {
  public:
    static uint8_t DATA[RF69_MAX_DATA_LEN]; // recv/xmit buf, including header & crc bytes
    static uint8_t DATALEN;
    static uint16_t SENDERID;
    static uint16_t TARGETID; // should match _address
    static uint8_t PAYLOADLEN;
    static uint8_t ACK_REQUESTED;
    static uint8_t ACK_RECEIVED; // should be polled immediately after sending a packet with ACK request
    static int16_t RSSI; // most accurate RSSI during reception (closest to the reception). RSSI of last packet.
    static uint8_t _mode; // should be protected?
    RFM69(uint8_t slaveSelectPin, uint8_t interruptPin, bool isRFM69HW, uint8_t interruptNum) //interruptNum is now deprecated
                : RFM69(slaveSelectPin, interruptPin, isRFM69HW){};
    RFM69(uint8_t slaveSelectPin=RF69_SPI_CS, uint8_t interruptPin=RF69_IRQ_PIN, bool isRFM69HW=false);
    bool initialize(uint8_t freqBand, uint16_t ID, uint8_t networkID=1, uint8_t slaveSelectPin=26, uint8_t interruptPin=12, bool isRFM69HW=false);
    void setAddress(uint16_t addr);
    void setNetwork(uint8_t networkID);
    bool canSend();
    virtual void send(uint16_t toAddress, const void* buffer, uint8_t bufferSize, bool requestACK=false);
    virtual bool sendWithRetry(uint16_t toAddress, const void* buffer, uint8_t bufferSize, uint8_t retries=2, uint8_t retryWaitTime=40); // 40ms roundtrip req for 61byte packets
    virtual bool receiveDone();
    bool ACKReceived(uint16_t fromNodeID);
    bool ACKRequested();
    virtual void sendACK(const void* buffer = "", uint8_t bufferSize=0);
    uint32_t getFrequency();
    void setFrequency(uint32_t freqHz);
    void encrypt(const char* key);
    void setCS(uint8_t newSPISlaveSelect);
    int16_t readRSSI(bool forceTrigger=false); // *current* signal strength indicator; e.g. < -90dBm says the frequency channel is free + ready to transmit
    void promiscuous(bool onOff=true);
    virtual void setHighPower(bool onOFF=true); // has to be called after initialize() for RFM69HW
    virtual void setPowerLevel(uint8_t level); // reduce/increase transmit power level
    void sleep();
    uint8_t readTemperature(uint8_t calFactor=0); // get CMOS temperature (8bit)
    void rcCalibration(); // calibrate the internal RC oscillator for use in wide temperature variations - see datasheet section [4.3.5. RC Timer Accuracy]
    uint8_t readReg(uint8_t addr);
    void writeReg(uint8_t addr, uint8_t val);
    void readAllRegs();
    void readAllRegsCompact();
  protected:
    static void isr0();
    void interruptHandler();
    virtual void interruptHook(uint8_t CTLbyte) {};
    static volatile bool _haveData;
    virtual void sendFrame(uint16_t toAddress, const void* buffer, uint8_t size, bool requestACK=false, bool sendACK=false);
    static RFM69* selfPointer;
    uint8_t _slaveSelectPin;
    uint8_t _interruptPin;
    uint8_t _interruptNum;
    uint16_t _address;
    bool _promiscuousMode;
    uint8_t _powerLevel;
    bool _isRFM69HW;
#if defined (SPCR) && defined (SPSR)
    uint8_t _SPCR;
    uint8_t _SPSR;
#endif
#ifdef SPI_HAS_TRANSACTION
  SPISettings _settings;
#endif
    virtual void receiveBegin();
    virtual void setMode(uint8_t mode);
    virtual void setHighPowerRegs(bool onOff);
    virtual void select();
    virtual void unselect();
};
